qbancoffee/imac_g3_ivad_board_init/ImacG3DVDisplayProperties/src/imacg3dvdisplayproperties/resources/keystone_stretch_top.png

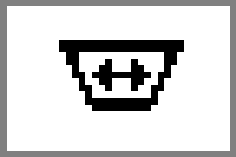
ImacG3DVDisplayProperties/src/imacg3dvdisplayproperties/resources/keystone_stretch_top.png
