qbancoffee/imac_g3_ivad_board_init/ImacG3DVDisplayProperties/src/imacg3dvdisplayproperties/resources/monitor.png

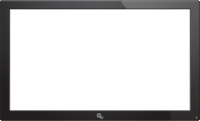
ImacG3DVDisplayProperties/src/imacg3dvdisplayproperties/resources/monitor.png
