qbancoffee/imac_g3_ivad_board_init/ImacG3DVDisplayProperties/src/imacg3dvdisplayproperties/resources/reduce_height.png

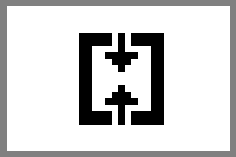
ImacG3DVDisplayProperties/src/imacg3dvdisplayproperties/resources/reduce_height.png
