qbancoffee/imac_g3_ivad_board_init/ImacG3DVDisplayProperties/src/imacg3dvdisplayproperties/resources/rotate_clockwise.png

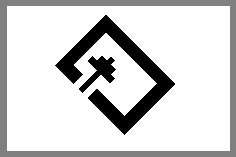
ImacG3DVDisplayProperties/src/imacg3dvdisplayproperties/resources/rotate_clockwise.png
