qbancoffee/imac_g3_ivad_board_init/images/analog_board.jpg

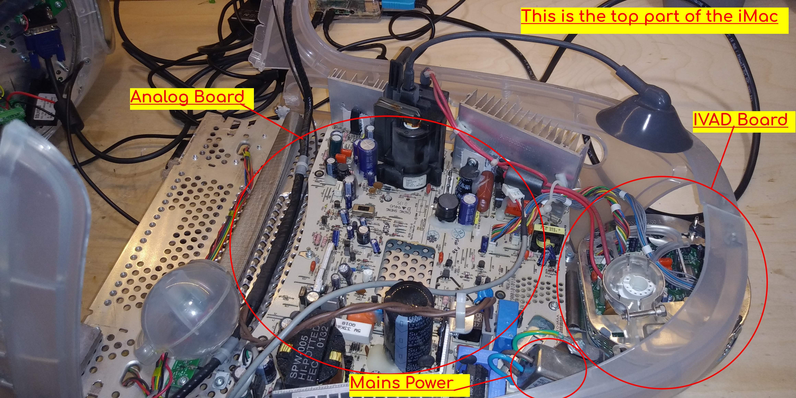
images/analog_board.jpg
