qbancoffee/imac_g3_ivad_board_init/images/analog_board_off.jpg

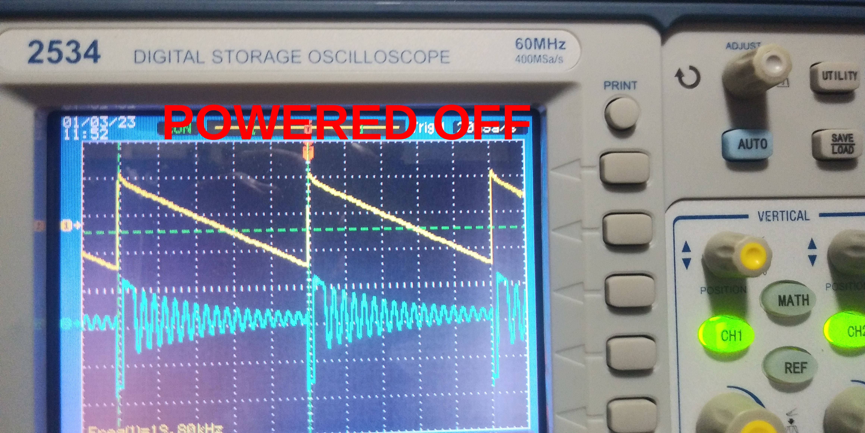
images/analog_board_off.jpg
