qbancoffee/imac_g3_ivad_board_init/images/analog_board_on.jpg

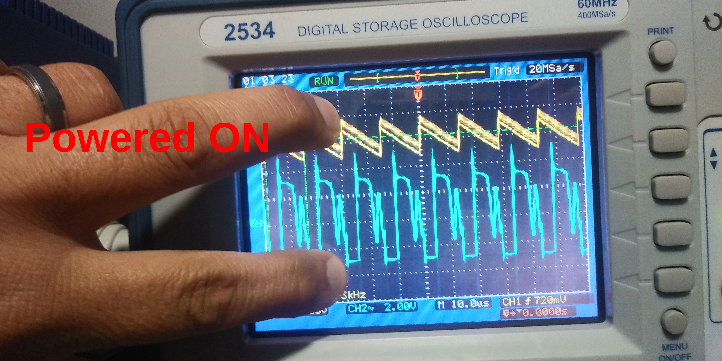
images/analog_board_on.jpg
