qbancoffee/imac_g3_ivad_board_init/images/arduino_uno_isp.png

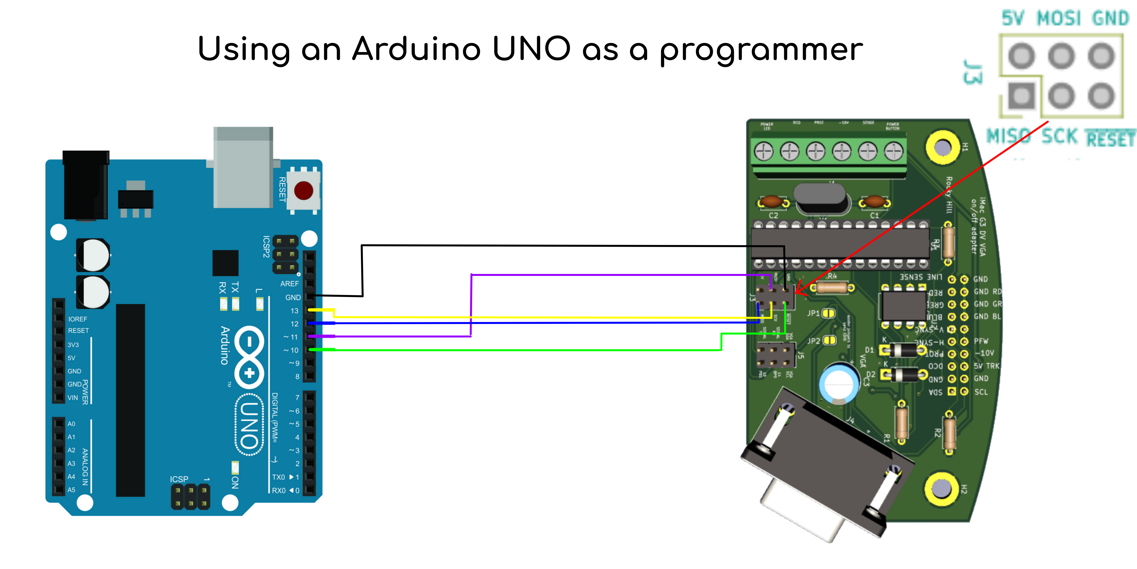
images/arduino_uno_isp.png
