qbancoffee/imac_g3_ivad_board_init/images/harness.jpg

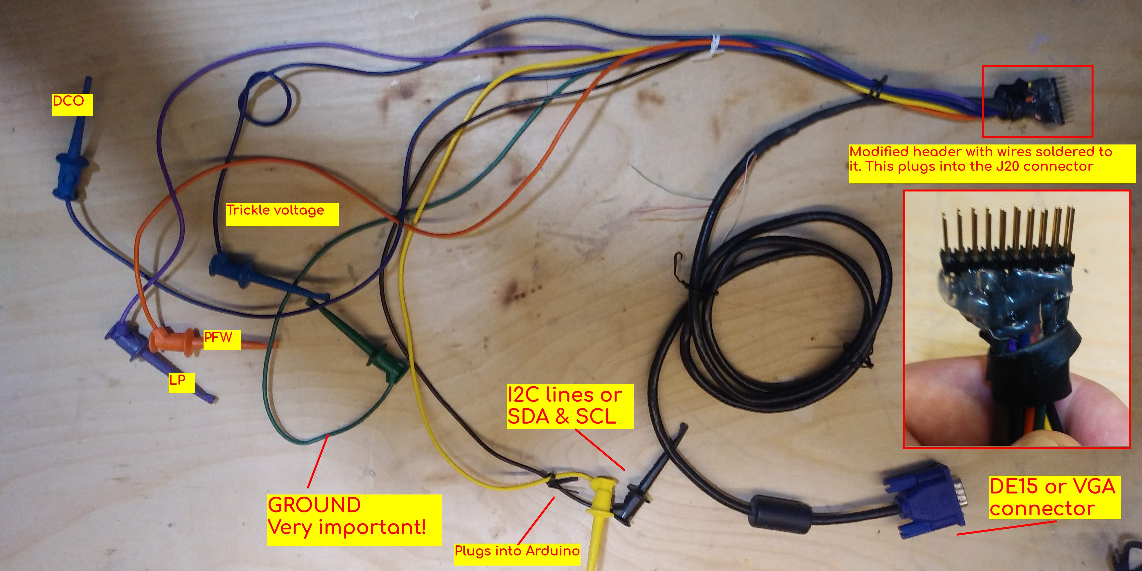
images/harness.jpg
