qbancoffee/imac_g3_ivad_board_init/images/imac_g3_adapter_boards.png

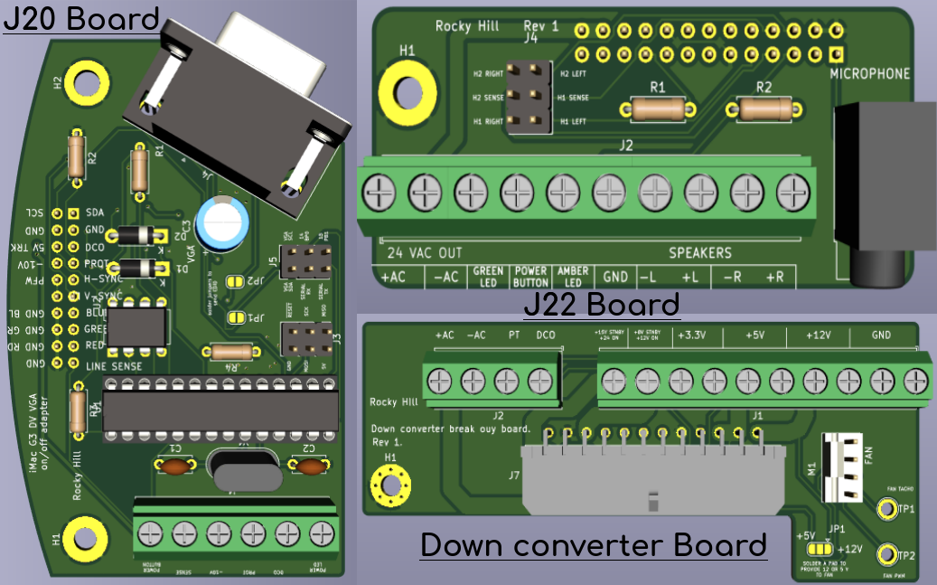
images/imac_g3_adapter_boards.png
