qbancoffee/imac_g3_ivad_board_init/images/J20_and_J22_in_view.jpg

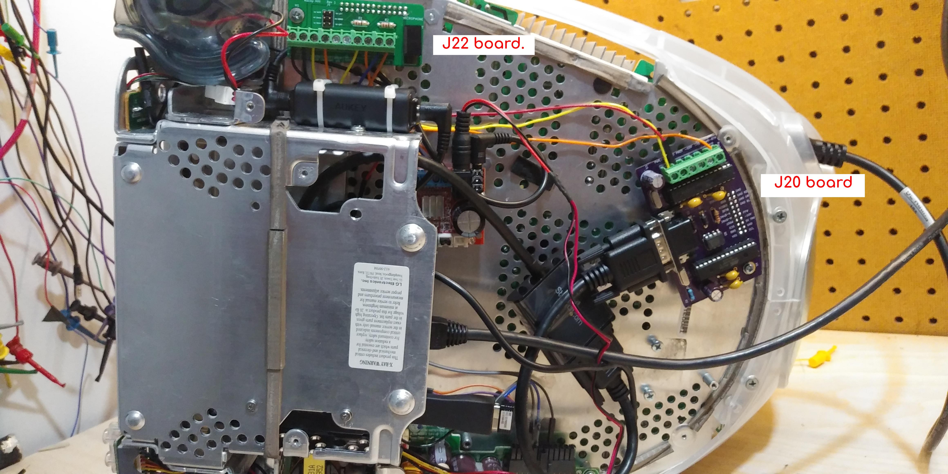
images/J20_and_J22_in_view.jpg
