qbancoffee/imac_g3_ivad_board_init/images/logic_board_and_downconverter_board.jpg

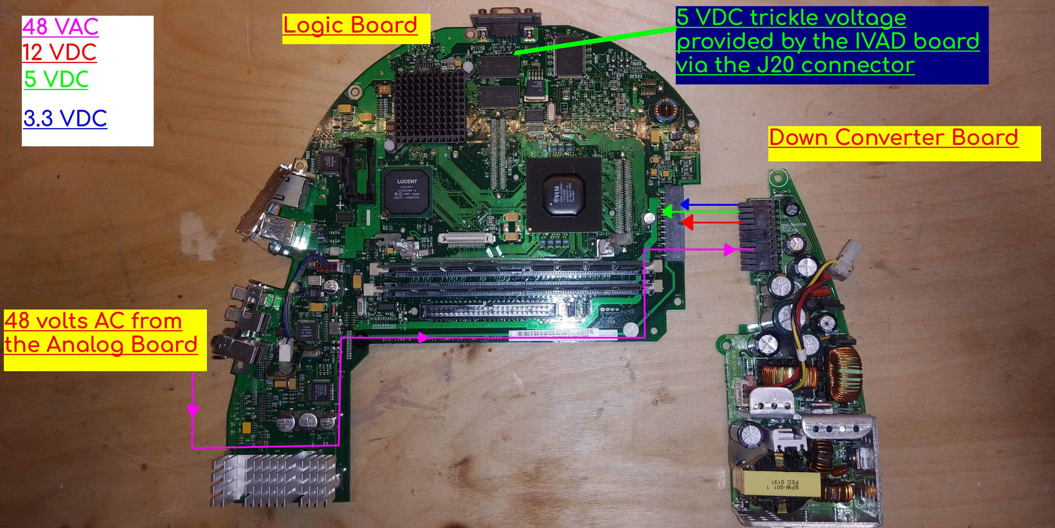
images/logic_board_and_downconverter_board.jpg
